nordseele/nordhat/hardware/images/20.jpg

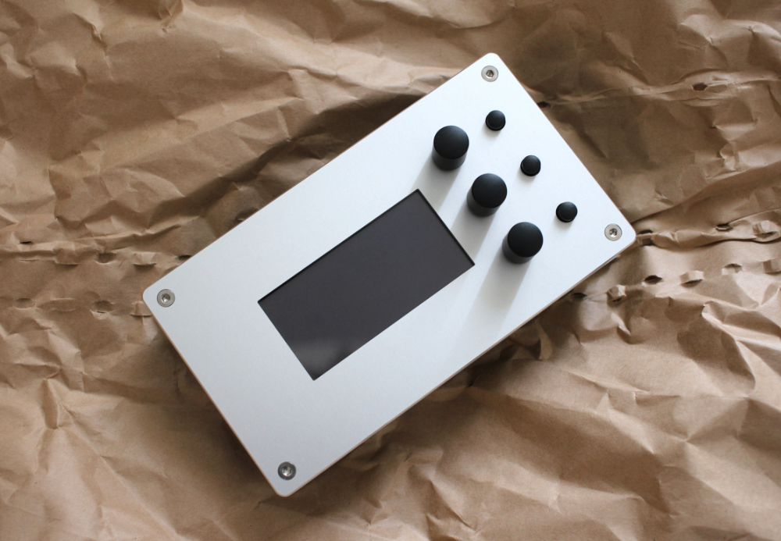
hardware/images/20.jpg
